astromaf/5-Inch-Electric-Model-Railway/Pictures/Loco_1.jpg

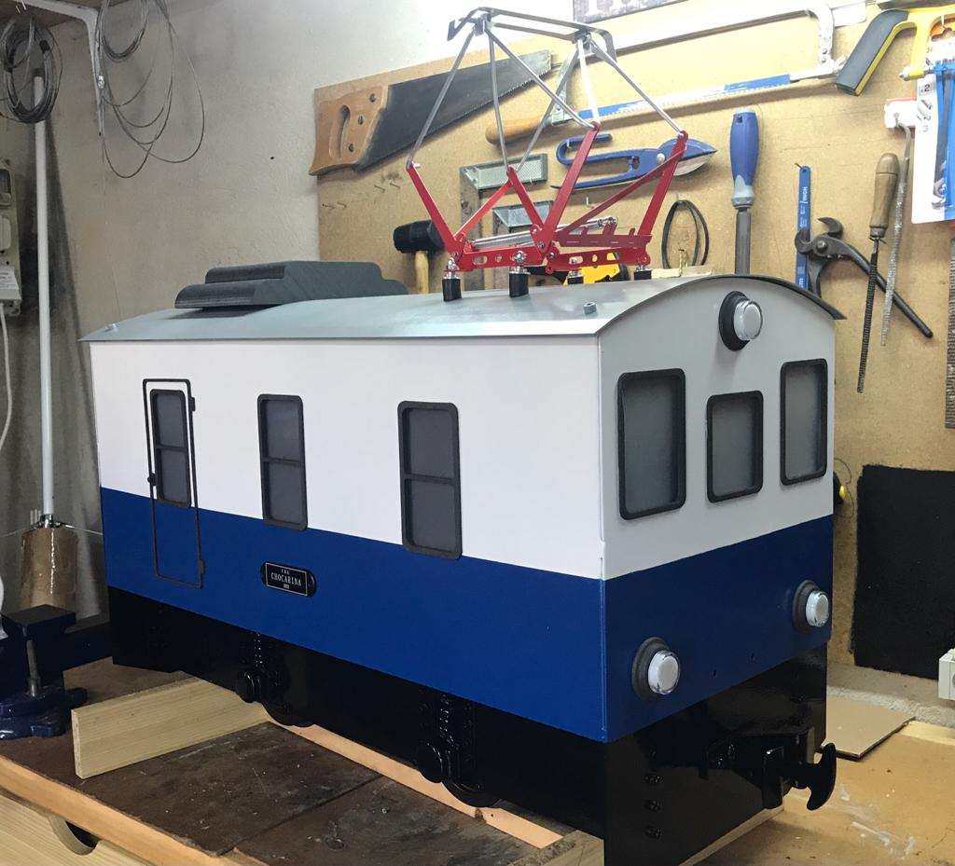
Pictures/Loco_1.jpg
