astromaf/5-Inch-Electric-Model-Railway/Pictures/Loco_3.jpg

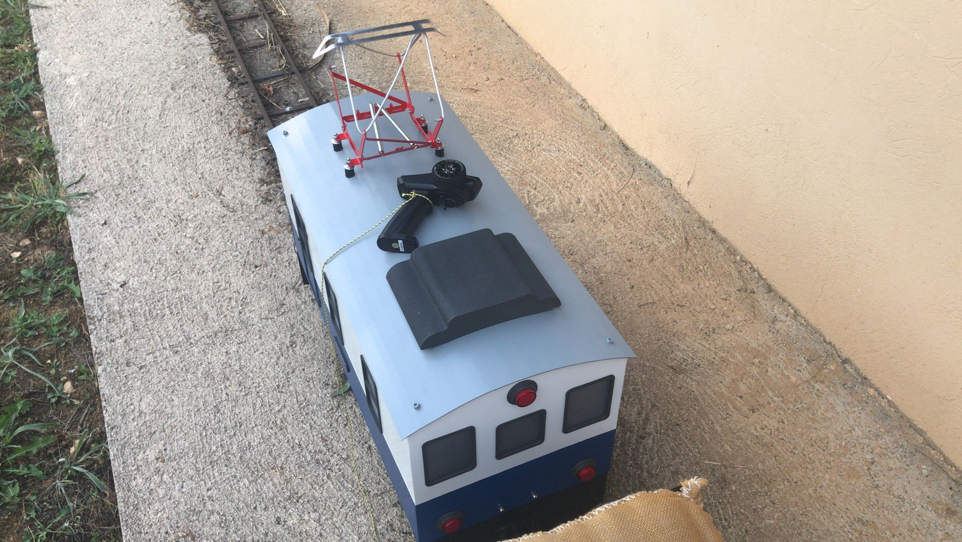
Pictures/Loco_3.jpg
