astromaf/5-Inch-Electric-Model-Railway/Pictures/turia_1.jpeg

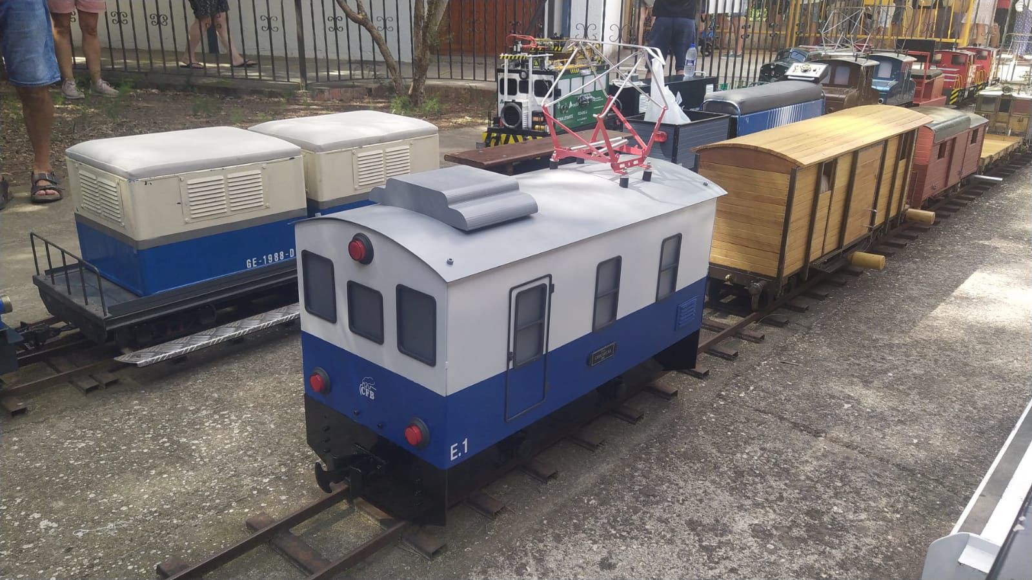
Pictures/turia_1.jpeg
