astromaf/5-Inch-Electric-Model-Railway/Pictures/turia_2.jpeg

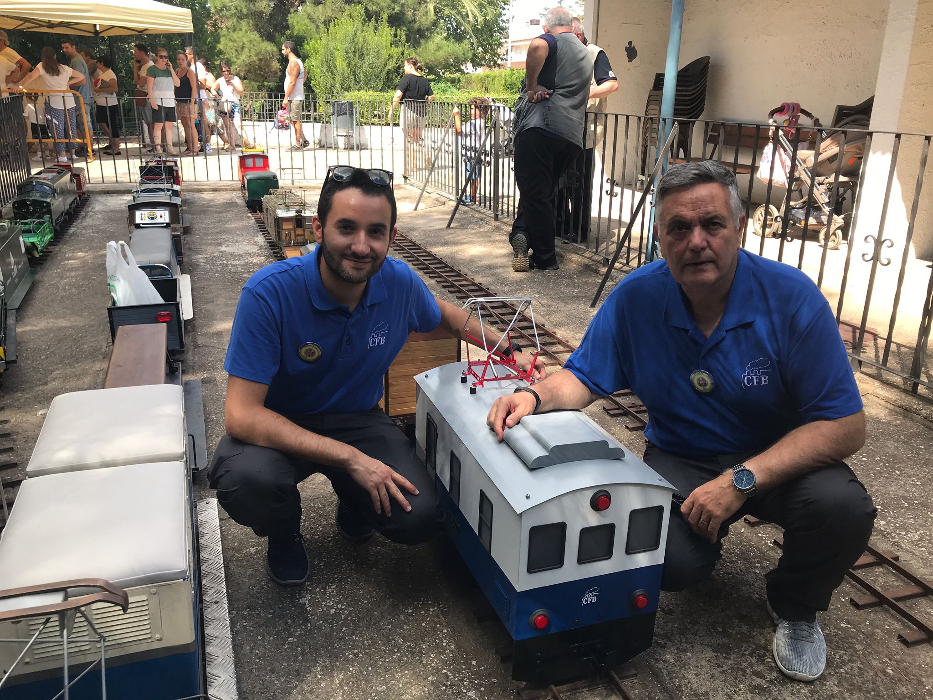
Pictures/turia_2.jpeg
