astromaf/5-Inch-Electric-Model-Railway/Electronics/PCB_test.jpg

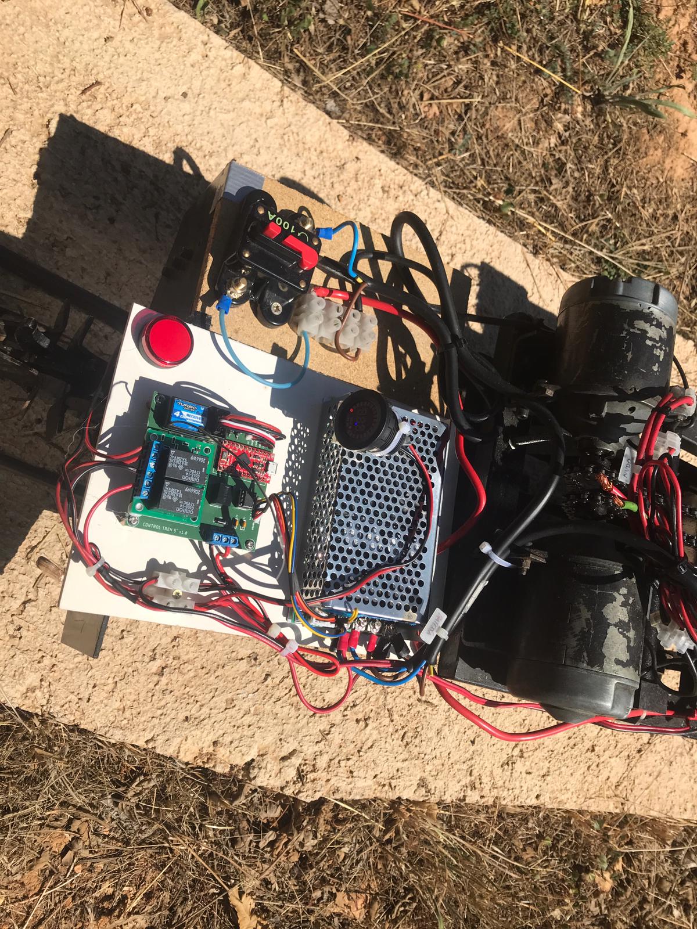
Electronics/PCB_test.jpg
